bnhovde/ir-graffiti/preview_cap.png

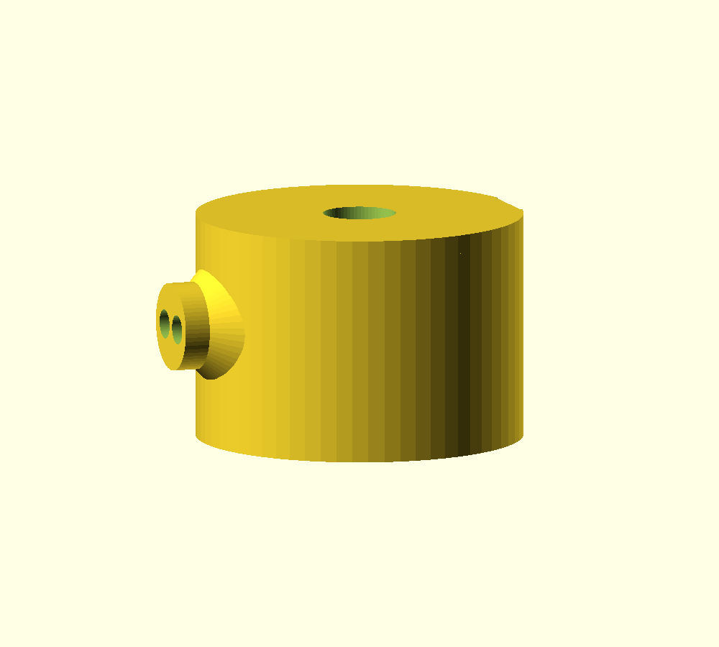
preview_cap.png
